TeodoraEnache/Proiect_Preamplificator_Audio/Schematic/Schematic/P1_CEF-PSpiceFiles/SCHEMATIC1/bias/bias.cir

** Profile: "SCHEMATIC1-bias"  [ C:\Users\Admin\Documents\etti\TCAD\CEF\l1\P1_CEF-PSpiceFiles\SCHEMATIC1\bias.sim ] 

** Creating circuit file "bias.cir" 
** WARNING: THIS AUTOMATICALLY GENERATED FILE MAY BE OVERWRITTEN BY SUBSEQUENT SIMULATIONS

*Libraries: 
* Profile Libraries :
* Local Libraries :
* From [PSPICE NETLIST] section of C:\SPB_Data\cdssetup\OrCAD_PSpice\17.2.0\PSpice.ini file:
.lib "nomd.lib" 

*Analysis directives: 
.OPTIONS ADVCONV
.PROBE64 V(alias(*)) I(alias(*)) W(alias(*)) D(alias(*)) NOISE(alias(*)) 
.INC "..\SCHEMATIC1.net" 


.END
