TeodoraEnache/Proiect_Preamplificator_Audio/Schematic/Schematic/P1_CEF-PSpiceFiles/SCHEMATIC1/P1/P1.cir

** Profile: "SCHEMATIC1-P1"  [ c:\users\admin\documents\etti\tcad\cef\l1\p1_cef-pspicefiles\schematic1\p1.sim ] 

** Creating circuit file "P1.cir" 
** WARNING: THIS AUTOMATICALLY GENERATED FILE MAY BE OVERWRITTEN BY SUBSEQUENT SIMULATIONS

*Libraries: 
* Profile Libraries :
* Local Libraries :
* From [PSPICE NETLIST] section of C:\SPB_Data\cdssetup\OrCAD_PSpice\17.2.0\PSpice.ini file:
.lib "nomd.lib" 

*Analysis directives: 
.TRAN  0 3ms 0 100ns 
.OPTIONS ADVCONV
.PROBE64 V(alias(*)) I(alias(*)) W(alias(*)) D(alias(*)) NOISE(alias(*)) 
.INC "..\SCHEMATIC1.net" 


.END
